xavierbradford/combat-led/led_master_esp32/arena_ui.h

// Arena web UI page (HTML/CSS/JS), split out into its own header on
// purpose: the Arduino IDE's automatic function-prototype generator
// only scans the .ino file, and its naive text scan gets confused by
// raw string literals that contain code-like text (e.g. the JS below
// has "(function () {" in it) if they live directly in the .ino -
// it can misparse that as real C++ and fail to compile. Keeping it in
// a .h file (a normal sketch tab) sidesteps that scanner entirely.
#pragma once

static const char INDEX_HTML[] PROGMEM = R"HTMLPAGE(
<!DOCTYPE html>
<html lang="en">
<head>
<meta charset="UTF-8">
<meta name="viewport" content="width=device-width, initial-scale=1, maximum-scale=1">
<title>Arena</title>
<style>
  :root {
    --brand: #1fa29b;
    --red: #d64545;
    --blue: #3b6fd6;
    --gray: #6b7280;
  }
  * { box-sizing: border-box; }
  html, body {
    margin: 0; padding: 0;
    background: #ffffff;
    font-family: -apple-system, BlinkMacSystemFont, "Segoe UI", Roboto, Helvetica, Arial, sans-serif;
    color: #1a1a1a;
  }
  .topbar {
    background: var(--brand);
    padding: 14px 16px;
    display: flex;
    justify-content: center;
    align-items: center;
  }
  .topbar svg { width: 100%; max-width: 480px; height: auto; display: block; }
  .topbar img { width: 100%; max-width: 400px; height: auto; display: block; }
  main { max-width: 480px; margin: 0 auto; padding: 20px 16px 40px; }
  .panel {
    border: 1px solid #e5e7eb;
    border-radius: 16px;
    padding: 24px 20px;
    text-align: center;
    box-shadow: 0 1px 3px rgba(0,0,0,0.06);
  }
  .phase-label {
    font-size: 14px;
    text-transform: uppercase;
    letter-spacing: 0.08em;
    color: var(--gray);
    margin-bottom: 6px;
  }
  .phase-name { font-size: 32px; font-weight: 700; margin-bottom: 4px; }
  .winner-banner { font-size: 22px; font-weight: 700; margin: 12px 0 4px; }
  .winner-banner.red { color: var(--red); }
  .winner-banner.blue { color: var(--blue); }
  .countdown-number { font-size: 56px; font-weight: 800; margin: 8px 0; }
  .buttons { display: flex; flex-direction: column; gap: 12px; margin-top: 20px; }
  .buttons.row { flex-direction: row; }
  button {
    flex: 1;
    font-size: 18px;
    font-weight: 600;
    padding: 16px 12px;
    border: none;
    border-radius: 12px;
    color: white;
    background: var(--brand);
    -webkit-tap-highlight-color: transparent;
  }
  button:active { opacity: 0.85; }
  button:disabled { opacity: 0.5; }
  button.red { background: var(--red); }
  button.blue { background: var(--blue); }
  button.gray { background: var(--gray); }
  .conn-status { text-align: center; font-size: 12px; color: var(--gray); margin-top: 16px; }
  .conn-status.offline { color: var(--red); }
</style>
</head>
<body>
  <div class="topbar">
    <img src="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" alt="STEM Coliseum">
  </div>
  <main>
    <div class="panel">
      <div class="phase-label">Current Phase</div>
      <div class="phase-name" id="phaseName">-</div>
      <div id="extra"></div>
      <div class="buttons" id="buttons"></div>
    </div>
    <div class="conn-status" id="connStatus">Connecting&hellip;</div>
  </main>
<script>
(function () {
  var phaseNameEl = document.getElementById('phaseName');
  var extraEl = document.getElementById('extra');
  var buttonsEl = document.getElementById('buttons');
  var connStatusEl = document.getElementById('connStatus');

  var state = { phase: null, winner: 'none', version: 0, countdownRemainingMs: 0, matchRemainingMs: 0, serverTime: 0 };
  var pendingAction = false;
  var matchTimeEl = null;

  // Clock skew between the client's wall clock and the ESP32's millis()
  // clock, plus the network one-way latency to it. serverTime is captured
  // in toJson() server-side, so remaining = matchRemainingMs -
  // (estimatedServerNow - serverTime) keeps the countdown synced despite
  // message delay and drift.
  var serverOffsetMs = 0;
  var oneWayLatencyMs = 15;

  function formatMs(ms) {
    var totalSec = Math.max(0, Math.ceil(ms / 1000));
    var m = Math.floor(totalSec / 60);
    var s = totalSec % 60;
    return (m < 10 ? '0' : '') + m + ':' + (s < 10 ? '0' : '') + s;
  }

  function estimatedMatchRemainingMs() {
    if (state.phase !== 'Match') return 0;
    var serverNow = Date.now() + serverOffsetMs;
    var remaining = state.matchRemainingMs - (serverNow - state.serverTime);
    return Math.max(0, remaining);
  }

  function buttonDefs() {
    switch (state.phase) {
      case 'Cleanup':
        return [{ action: 'endCleanup', label: 'End Cleanup' }];
      case 'Ready':
        return [{ action: 'startMatch', label: 'Start Match' }];
      case 'Countdown':
        return [];
      case 'Match':
        return [
          { action: 'redWin', label: 'Red Win', cls: 'red' },
          { action: 'blueWin', label: 'Blue Win', cls: 'blue' },
          { action: 'judges', label: 'Judges', cls: 'gray' }
        ];
      case 'Judging':
        return [
          { action: 'redWin', label: 'Red Win', cls: 'red' },
          { action: 'blueWin', label: 'Blue Win', cls: 'blue' }
        ];
      case 'Announcement':
        return [{ action: 'newMatch', label: 'Begin Cleanup' }];
      default:
        return [];
    }
  }

  function render() {
    phaseNameEl.textContent = state.phase || '-';
    extraEl.innerHTML = '';
    buttonsEl.innerHTML = '';
    buttonsEl.className = 'buttons';

    if (state.phase === 'Countdown') {
      var secs = Math.max(0, Math.ceil(state.countdownRemainingMs / 1000));
      var div = document.createElement('div');
      div.className = 'countdown-number';
      div.textContent = secs;
      extraEl.appendChild(div);
    }

    if (state.phase === 'Match') {
      var label = document.createElement('div');
      label.className = 'phase-label';
      label.textContent = 'Time Remaining';
      extraEl.appendChild(label);

      matchTimeEl = document.createElement('div');
      matchTimeEl.className = 'countdown-number';
      matchTimeEl.textContent = formatMs(estimatedMatchRemainingMs());
      extraEl.appendChild(matchTimeEl);
    } else {
      matchTimeEl = null;
    }

    if (state.phase === 'Announcement' && state.winner !== 'none') {
      var banner = document.createElement('div');
      banner.className = 'winner-banner ' + state.winner;
      banner.textContent = (state.winner === 'red' ? 'RED' : 'BLUE') + ' WINS';
      extraEl.appendChild(banner);
    }

    var defs = buttonDefs();
    if (defs.length > 1) buttonsEl.className = 'buttons row';
    defs.forEach(function (d) {
      var btn = document.createElement('button');
      btn.textContent = d.label;
      if (d.cls) btn.className = d.cls;
      btn.disabled = pendingAction;
      btn.onclick = function () { sendAction(d.action); };
      buttonsEl.appendChild(btn);
    });
  }

  function applyState(s) {
    state.phase = s.phase;
    state.winner = s.winner;
    state.version = s.version;
    state.countdownRemainingMs = s.countdownRemainingMs || 0;
    if (typeof s.matchRemainingMs === 'number') state.matchRemainingMs = s.matchRemainingMs;
    if (typeof s.serverTime === 'number') {
      // serverTime is the ESP32's millis() when the snapshot was built.
      // Anchor the client clock to it: offset = serverTime - (receive
      // time), backed off by the measured one-way latency.
      state.serverTime = s.serverTime;
      serverOffsetMs = state.serverTime - (Date.now() - oneWayLatencyMs);
    }
    render();
  }

  function sendAction(action) {
    if (pendingAction) return;
    pendingAction = true;
    render();
    fetch('/api/action', {
      method: 'POST',
      headers: { 'Content-Type': 'application/json' },
      body: JSON.stringify({ action: action, version: state.version })
    }).then(function (res) {
      return res.json().then(function (body) { return body; });
    }).then(function (body) {
      // Whether accepted or rejected (409 = someone else already acted
      // first), the response body is always the authoritative current
      // state - apply it directly rather than waiting on the websocket.
      applyState(body);
    }).catch(function () {
      // network hiccup - websocket reconnect / poll fallback will resync
    }).finally(function () {
      pendingAction = false;
      render();
    });
  }

  var ws;
  var wsReconnectTimer;

  function connectWs() {
    var proto = location.protocol === 'https:' ? 'wss' : 'ws';
    ws = new WebSocket(proto + '://' + location.host + '/ws');
    ws.onopen = function () {
      connStatusEl.textContent = 'Connected';
      connStatusEl.className = 'conn-status';
    };
    ws.onmessage = function (evt) {
      try { applyState(JSON.parse(evt.data)); } catch (e) {}
    };
    ws.onclose = function () {
      connStatusEl.textContent = 'Reconnecting\u2026';
      connStatusEl.className = 'conn-status offline';
      clearTimeout(wsReconnectTimer);
      wsReconnectTimer = setTimeout(connectWs, 1000);
    };
    ws.onerror = function () { ws.close(); };
  }

  // Belt-and-suspenders fallback: some phones throttle background
  // network activity, which can leave a websocket silently stuck. Poll
  // the plain HTTP state endpoint periodically so a device always
  // self-corrects even if its socket died quietly. The round-trip time
  // is also measured here to keep the match countdown clock in sync.
  setInterval(function () {
    var t0 = Date.now();
    fetch('/api/state').then(function (r) { return r.json(); }).then(function (s) {
      var rtt = Date.now() - t0;
      if (rtt > 0) oneWayLatencyMs = rtt / 2;
      applyState(s);
    }).catch(function () {});
  }, 5000);

  // Smooth 1s match countdown between state pushes, anchored to the
  // last known server clock rather than only updating on message arrive.
  setInterval(function () {
    if (matchTimeEl) matchTimeEl.textContent = formatMs(estimatedMatchRemainingMs());
  }, 200);

  connectWs();
  render();
})();
</script>
</body>
</html>
)HTMLPAGE";
